ShulzLab/MORJ/electromechanical/3D_files/optical_rotary_joint/roller_bearing/outer_grove.SLDPRT

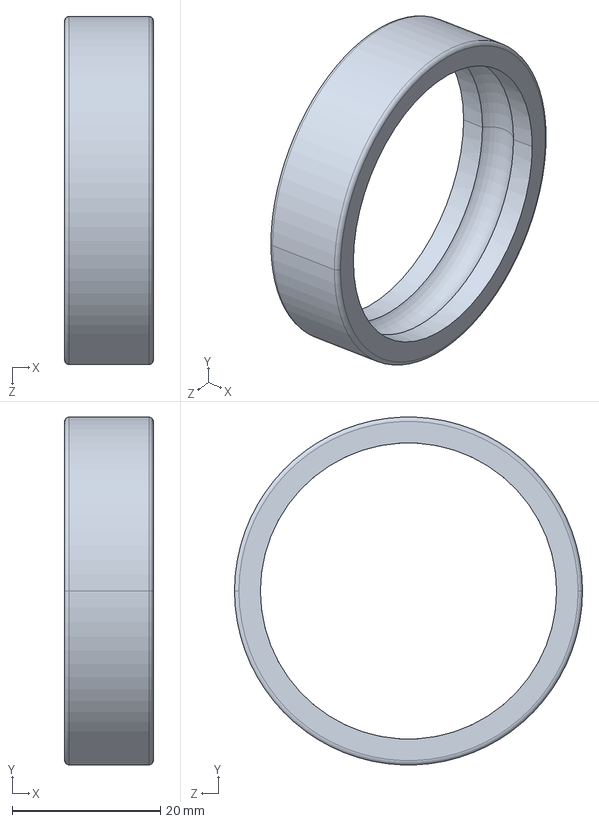
[picture p16: CAD file, 2022-12-15]
electromechanical/3D_files/optical_rotary_joint/roller_bearing/outer_grove.SLDPRT
12.0 x 47.0 x 47.0 mm
