ShulzLab/MORJ/electromechanical/3D_files/downstream_optical_assembly/Fiber_body.SLDPRT

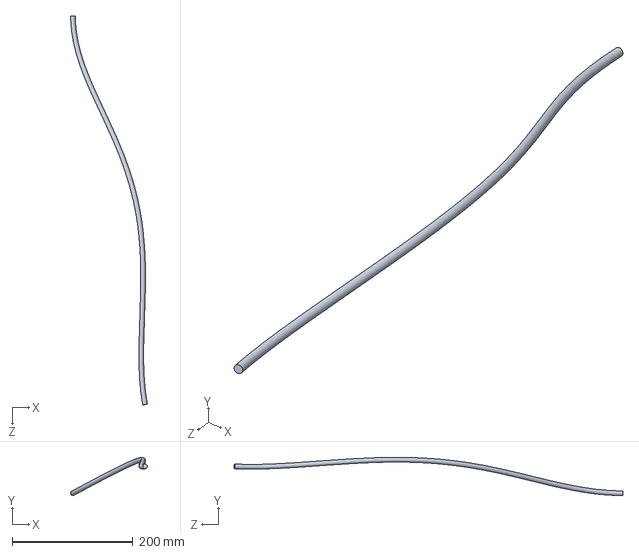
[picture p17: CAD file, 2022-12-15]
electromechanical/3D_files/downstream_optical_assembly/Fiber_body.SLDPRT
127.3 x 63.4 x 645.2 mm
