ShulzLab/MORJ/electromechanical/3D_files/electrical_rotary_joint/dovetail_fixed_body.SLDPRT

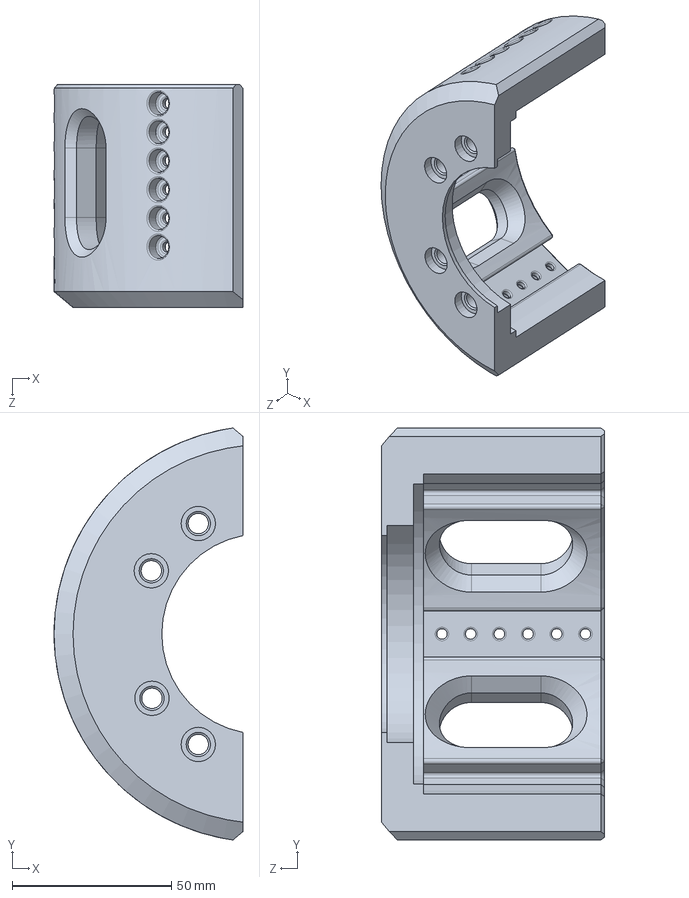
[picture p18: CAD file, 2022-12-15]
electromechanical/3D_files/electrical_rotary_joint/dovetail_fixed_body.SLDPRT
59.2 x 129.2 x 70.0 mm
