ShulzLab/MORJ/electromechanical/3D_files/motor_controller/proto_board.SLDPRT

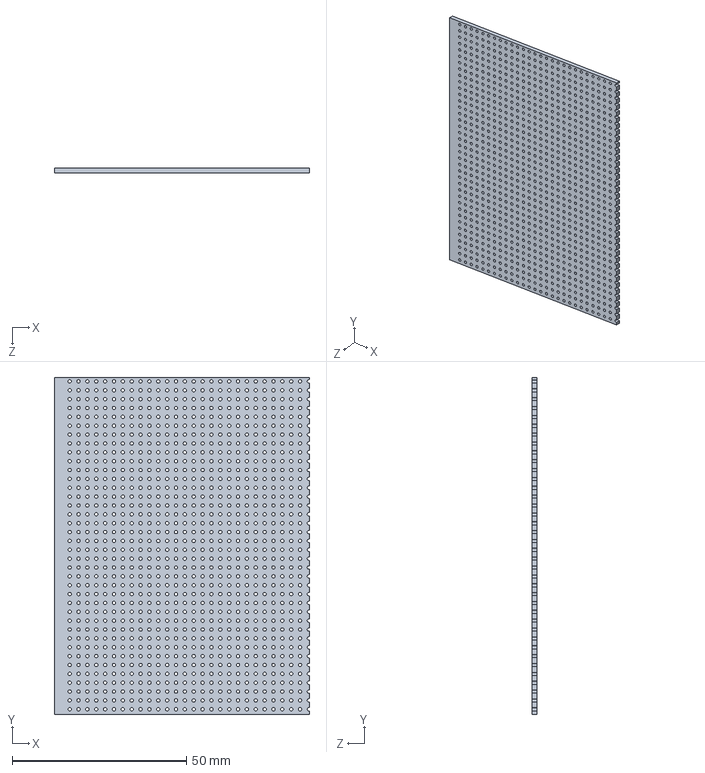
[picture p19: CAD file, 2022-12-15]
electromechanical/3D_files/motor_controller/proto_board.SLDPRT
73.2 x 96.6 x 1.54 mm
