ShulzLab/MORJ/electromechanical/3D_files/motor_system/Nema23_holder.SLDPRT

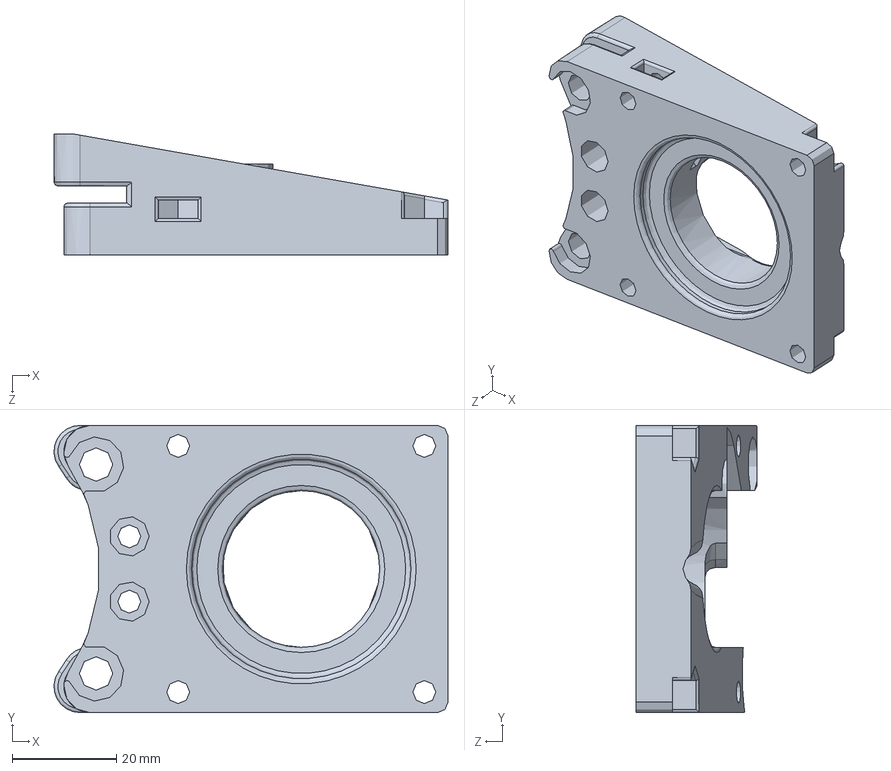
[picture p20: CAD file, 2022-12-15]
electromechanical/3D_files/motor_system/Nema23_holder.SLDPRT
75.5 x 55.0 x 23.2 mm
