ShulzLab/MORJ/electromechanical/3D_files/optical_rotary_joint/endplate.SLDPRT

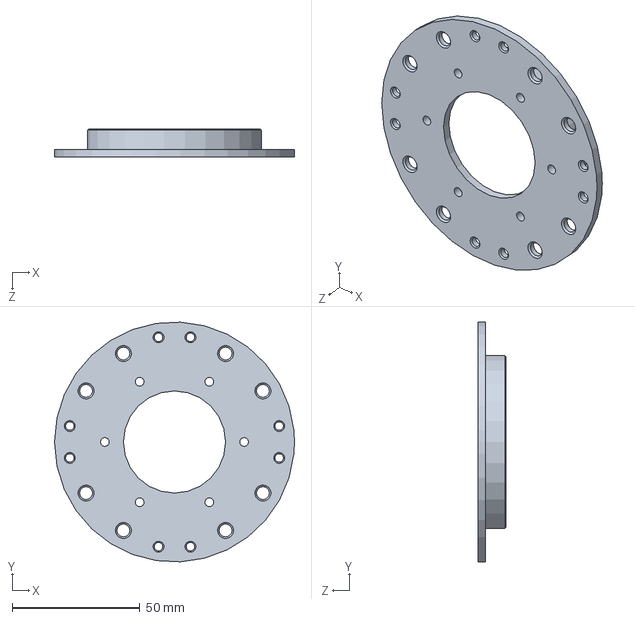
[picture p21: CAD file, 2022-12-15]
electromechanical/3D_files/optical_rotary_joint/endplate.SLDPRT
94.0 x 93.9 x 11.0 mm
