ShulzLab/MORJ/electromechanical/3D_files/upstream_optical_assembly/Lens.SLDPRT

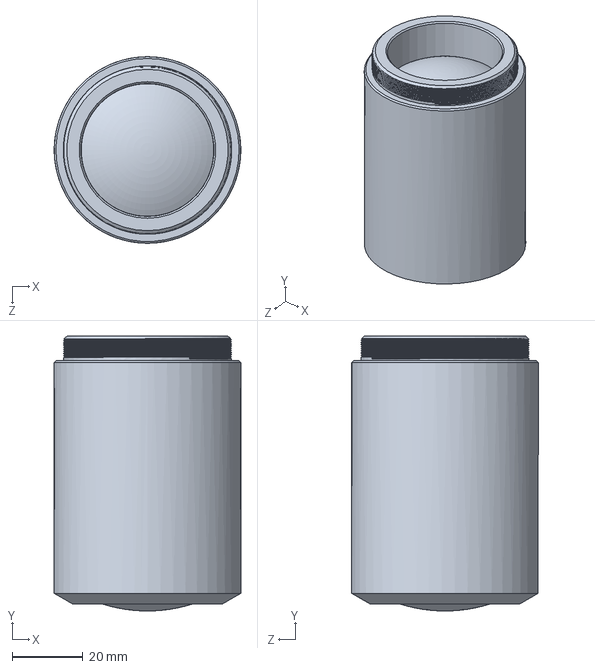
[picture p22: CAD file, 2022-12-15]
electromechanical/3D_files/upstream_optical_assembly/Lens.SLDPRT
52.9 x 78.0 x 52.9 mm
