ShulzLab/MORJ/electromechanical/3D_files/xyz_adjustment_system/focus_adjuster_proxy.SLDPRT

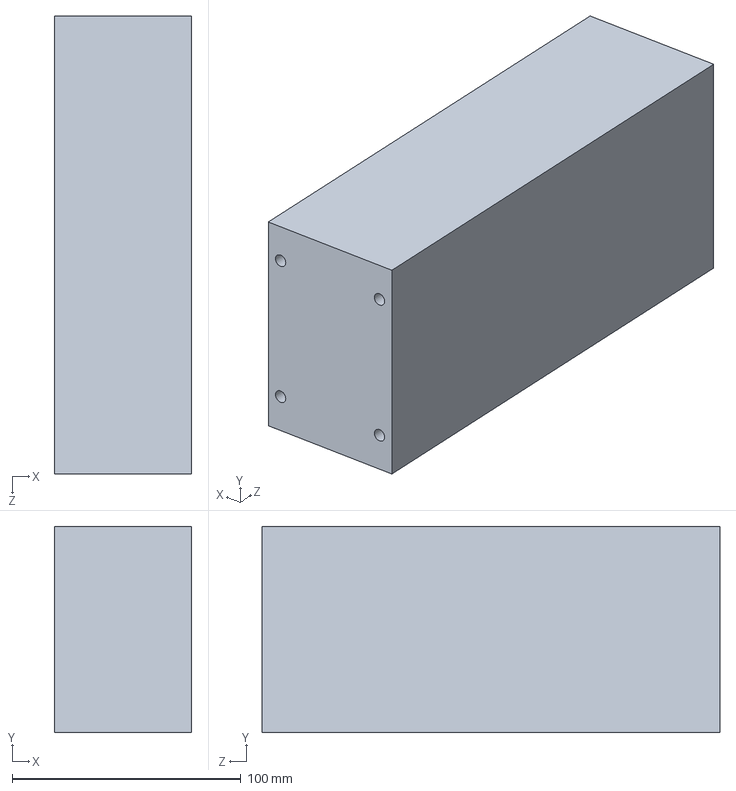
[picture p23: CAD file, 2022-12-15]
electromechanical/3D_files/xyz_adjustment_system/focus_adjuster_proxy.SLDPRT
60.0 x 90.0 x 200.0 mm
