ShulzLab/MORJ/electromechanical/3D_files/electrical_rotary_joint/dovetail_mobile_body.SLDPRT

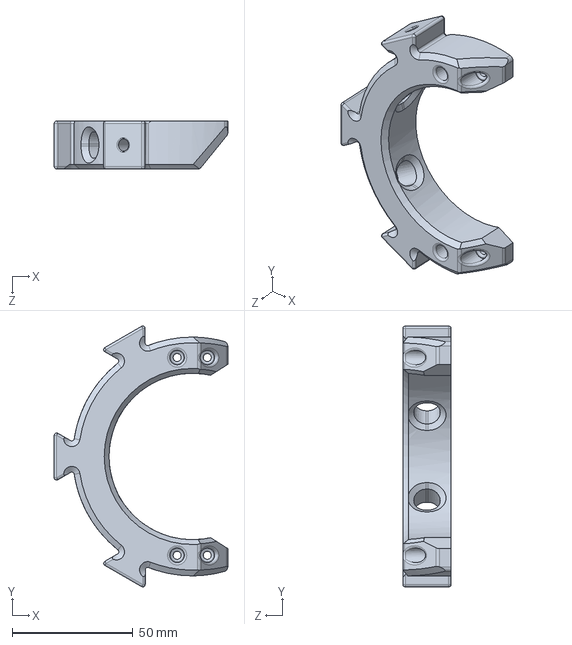
[picture p24: CAD file, 2022-12-15]
electromechanical/3D_files/electrical_rotary_joint/dovetail_mobile_body.SLDPRT
72.0 x 108.2 x 20.0 mm
