ShulzLab/MORJ/electromechanical/3D_files/motor_controller/connectors_opening_plate.SLDPRT

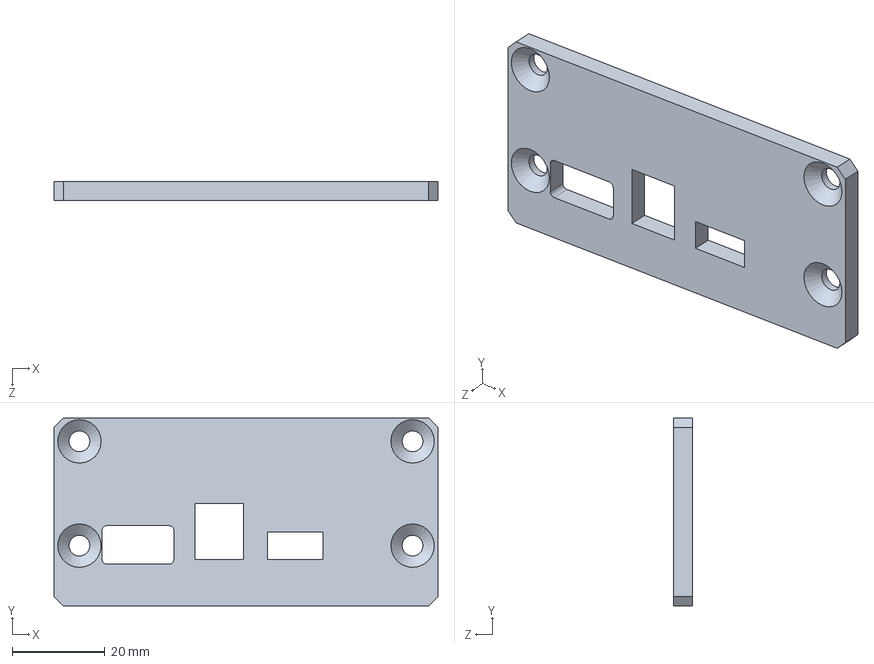
[picture p25: CAD file, 2022-12-15]
electromechanical/3D_files/motor_controller/connectors_opening_plate.SLDPRT
83.0 x 40.5 x 4.00 mm
