ShulzLab/MORJ/electromechanical/3D_files/motor_system/petitRoulementPlastique.SLDPRT

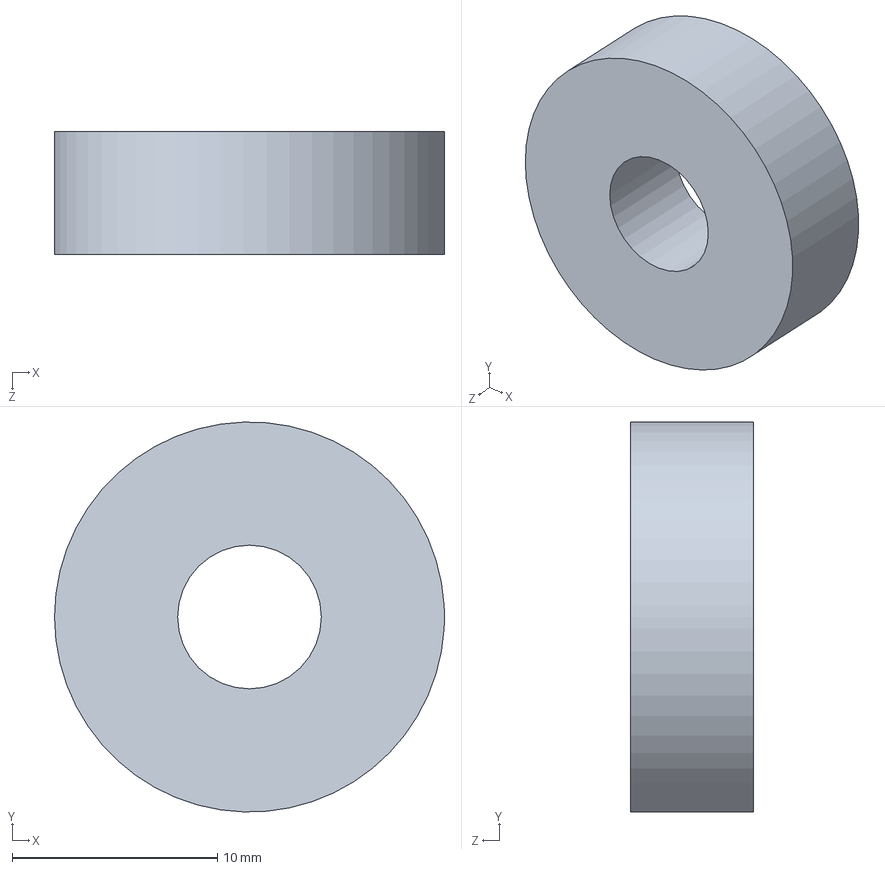
[picture p26: CAD file, 2022-12-15]
electromechanical/3D_files/motor_system/petitRoulementPlastique.SLDPRT
19.0 x 19.0 x 6.00 mm
