ShulzLab/MORJ/electromechanical/3D_files/optical_rotary_joint/roller_bearing/roller_ball.SLDPRT

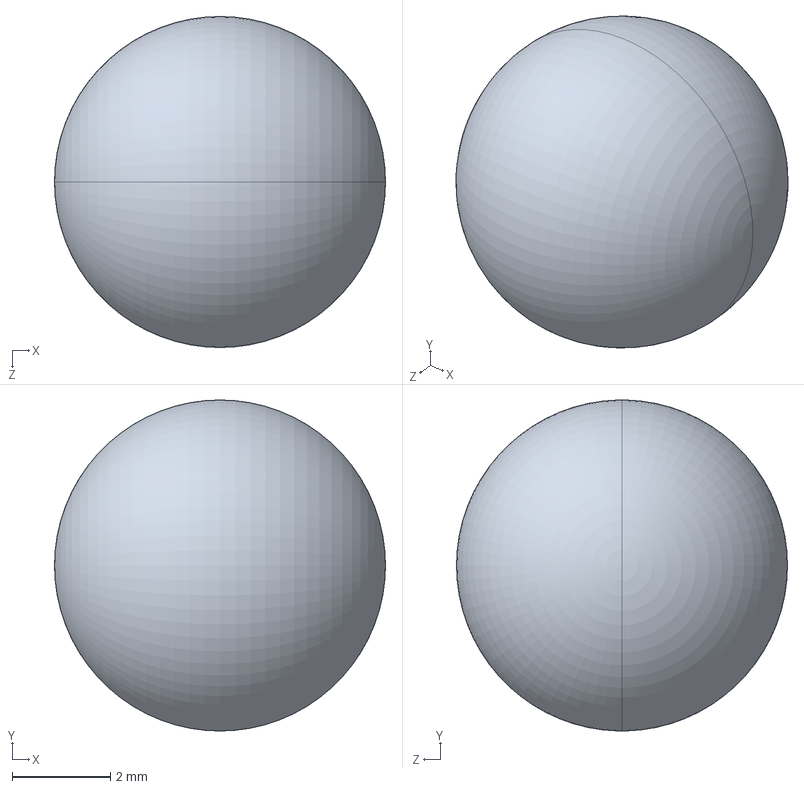
[picture p27: CAD file, 2022-12-15]
electromechanical/3D_files/optical_rotary_joint/roller_bearing/roller_ball.SLDPRT
6.75 x 6.75 x 6.75 mm
