ShulzLab/MORJ/electromechanical/3D_files/upstream_optical_assembly/Lens_hood.SLDPRT

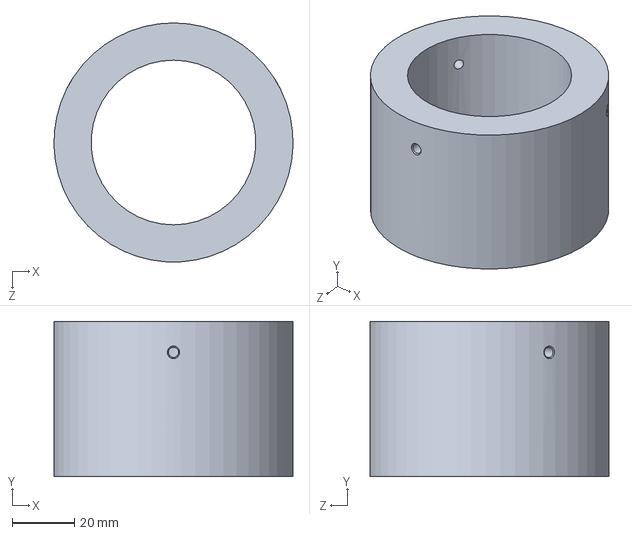
[picture p28: CAD file, 2022-12-15]
electromechanical/3D_files/upstream_optical_assembly/Lens_hood.SLDPRT
77.1 x 50.0 x 77.1 mm
