ShulzLab/MORJ/electromechanical/3D_files/xyz_adjustment_system/right_lateral_focus_holder.SLDPRT

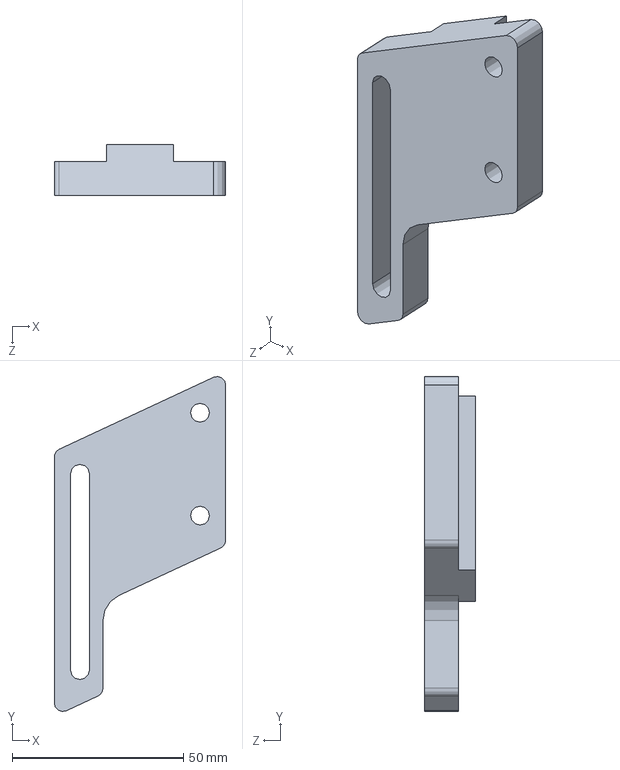
[picture p29: CAD file, 2022-12-15]
electromechanical/3D_files/xyz_adjustment_system/right_lateral_focus_holder.SLDPRT
50.0 x 97.7 x 15.0 mm
