ShulzLab/MORJ/electromechanical/3D_files/electrical_rotary_joint/driving_ring.SLDPRT

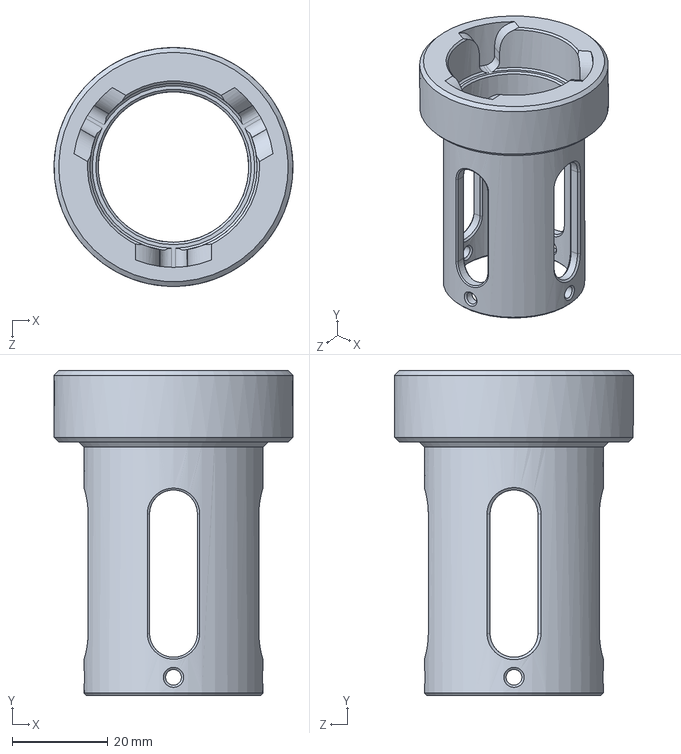
[picture p30: CAD file, 2022-12-15]
electromechanical/3D_files/electrical_rotary_joint/driving_ring.SLDPRT
50.0 x 68.0 x 50.0 mm
