ShulzLab/MORJ/electromechanical/3D_files/motor_controller/attachment_plate.SLDPRT

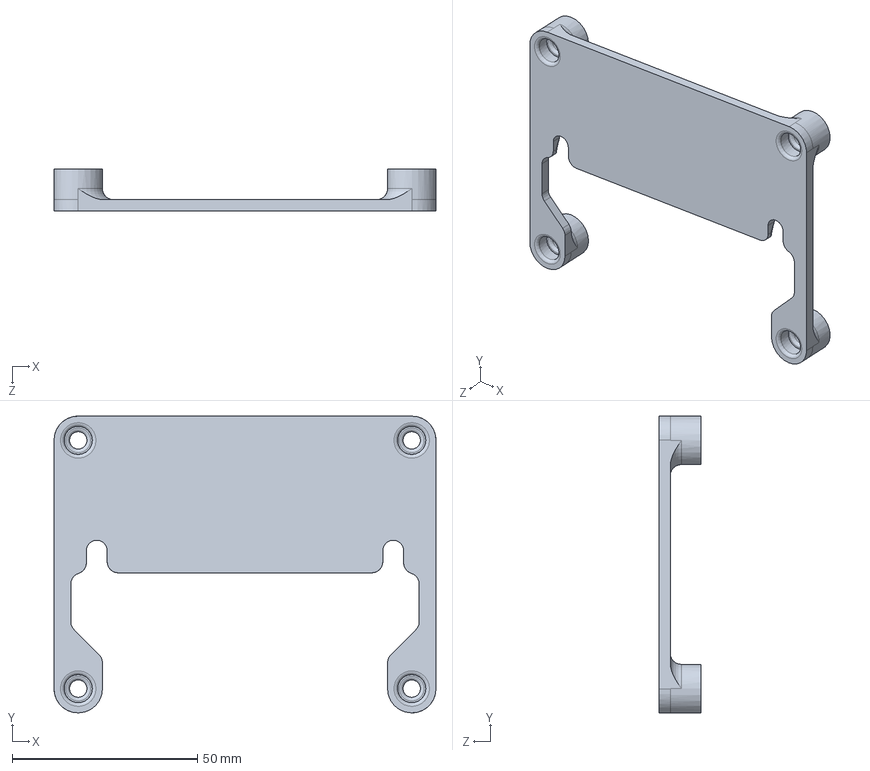
[picture p31: CAD file, 2022-12-15]
electromechanical/3D_files/motor_controller/attachment_plate.SLDPRT
103.1 x 80.1 x 11.2 mm
