ShulzLab/MORJ/electromechanical/3D_files/motor_system/StepperMotor_nema17.SLDPRT

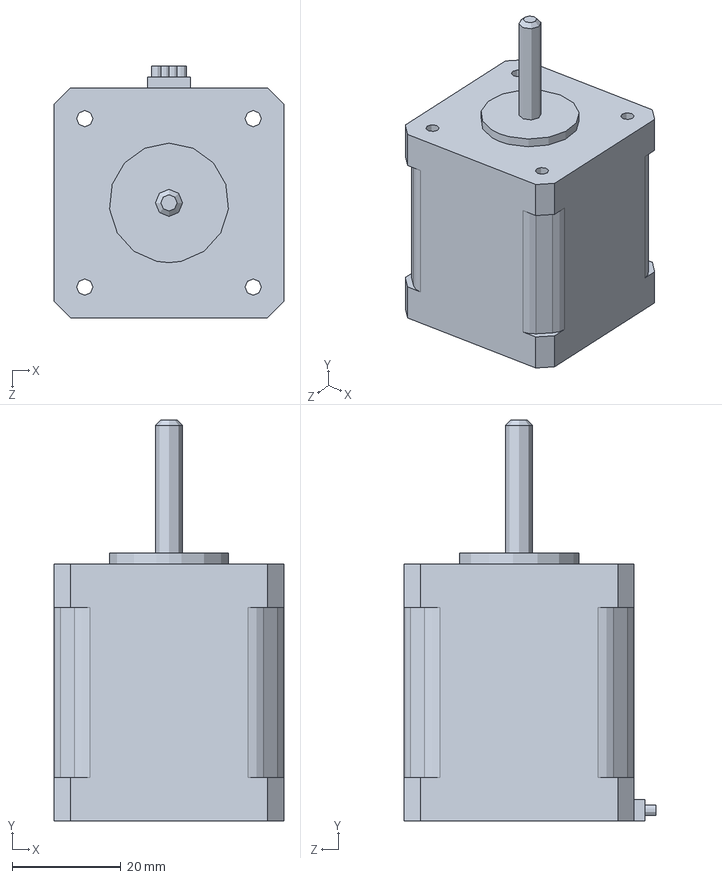
[picture p32: CAD file, 2022-12-15]
electromechanical/3D_files/motor_system/StepperMotor_nema17.SLDPRT
42.3 x 73.8 x 46.3 mm
