ShulzLab/MORJ/electromechanical/3D_files/optical_rotary_joint/roller_bearing/inner_grove.SLDPRT

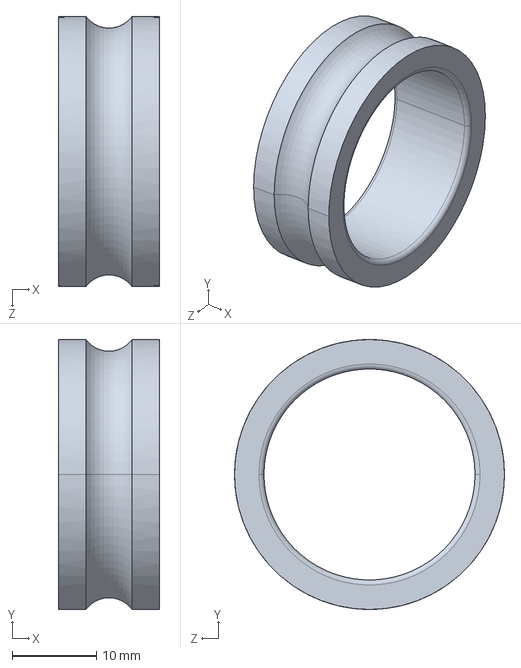
[picture p33: CAD file, 2022-12-15]
electromechanical/3D_files/optical_rotary_joint/roller_bearing/inner_grove.SLDPRT
12.0 x 32.0 x 32.0 mm
