ShulzLab/MORJ/electromechanical/3D_files/xyz_adjustment_system/BlocAdaptation.sldprt

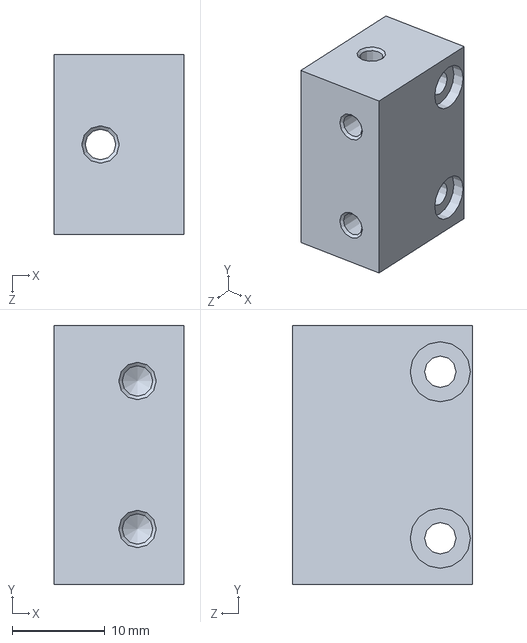
[picture p34: CAD file, 2022-12-15]
electromechanical/3D_files/xyz_adjustment_system/BlocAdaptation.sldprt
14.0 x 28.0 x 19.5 mm
