ShulzLab/MORJ/electromechanical/3D_files/electrical_rotary_joint/electrical_slip_ring_Jinpat_ LPT038-6.SLDPRT

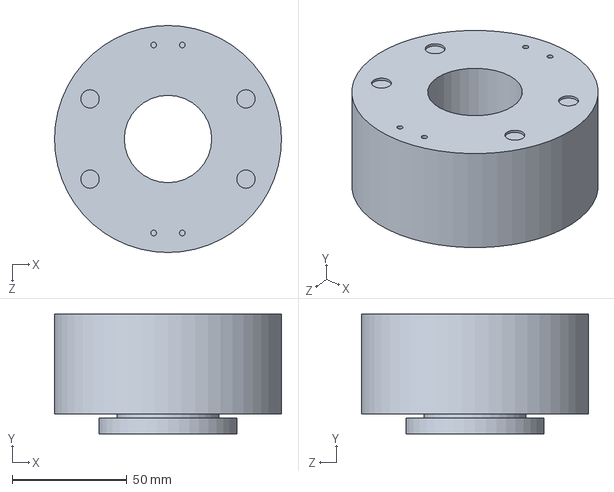
[picture p35: CAD file, 2022-12-15]
electromechanical/3D_files/electrical_rotary_joint/electrical_slip_ring_Jinpat_ LPT038-6.SLDPRT
99.0 x 52.3 x 99.0 mm
