ShulzLab/MORJ/electromechanical/3D_files/motor_controller/USB_port.SLDPRT

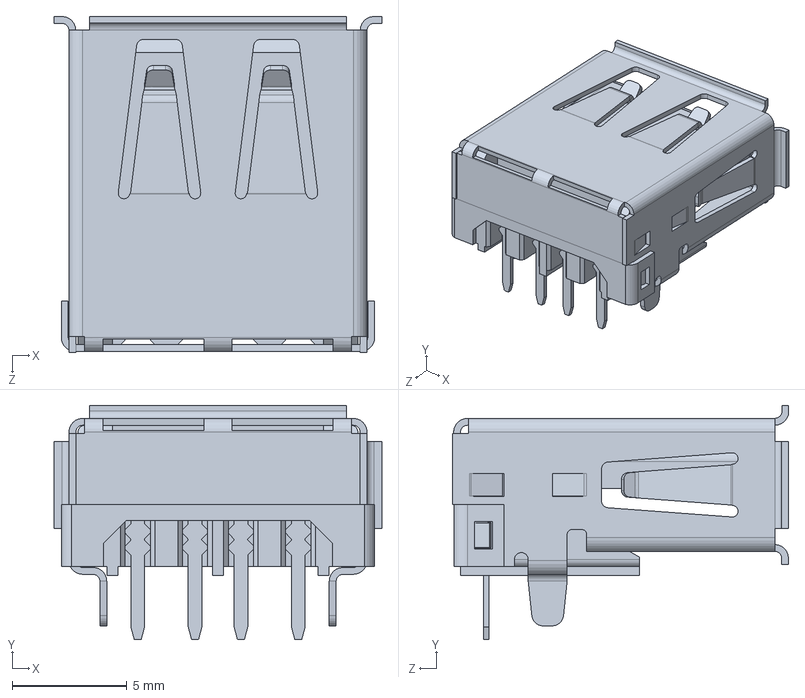
[picture p36: CAD file, 2022-12-15]
electromechanical/3D_files/motor_controller/USB_port.SLDPRT
14.3 x 10.2 x 14.6 mm
