ShulzLab/MORJ/electromechanical/3D_files/motor_system/Plot_Roulementplastique.SLDPRT

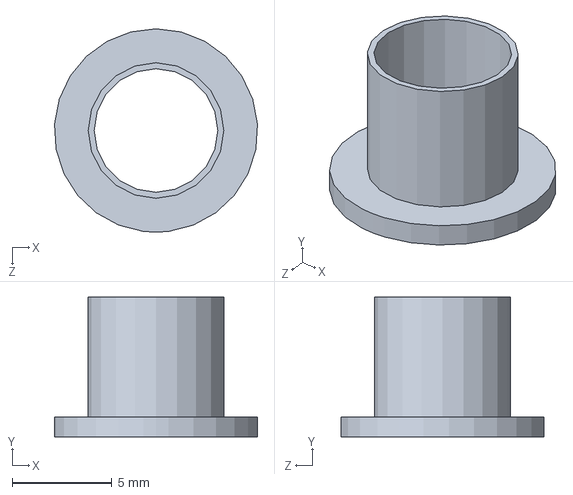
[picture p37: CAD file, 2022-12-15]
electromechanical/3D_files/motor_system/Plot_Roulementplastique.SLDPRT
10.2 x 7.00 x 10.2 mm
