ShulzLab/MORJ/electromechanical/3D_files/xyz_adjustment_system/Top_focus_holder.SLDPRT

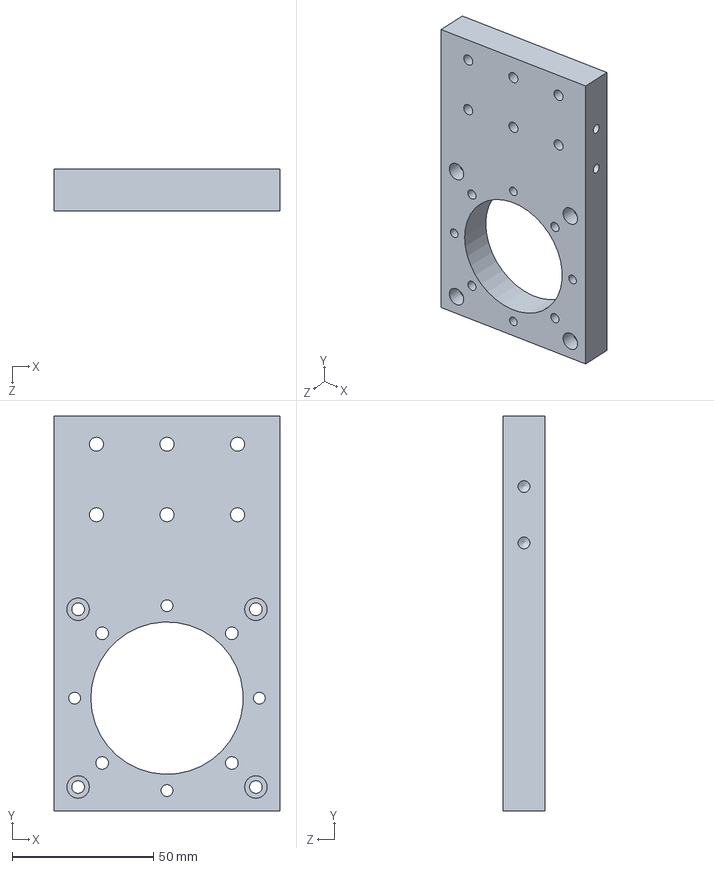
[picture p38: CAD file, 2022-12-15]
electromechanical/3D_files/xyz_adjustment_system/Top_focus_holder.SLDPRT
80.0 x 140.0 x 15.0 mm
