ShulzLab/MORJ/electromechanical/3D_files/optical_rotary_joint/adjustable_height_rotative_body.SLDPRT

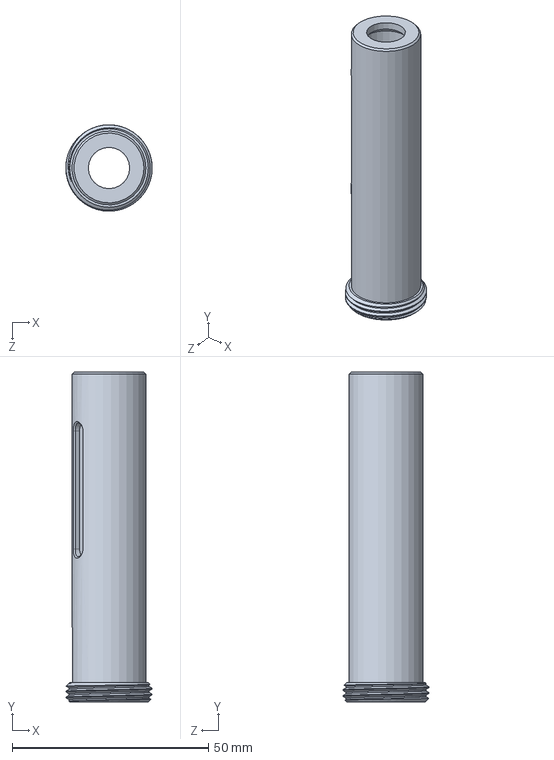
[picture p39: CAD file, 2022-12-15]
electromechanical/3D_files/optical_rotary_joint/adjustable_height_rotative_body.SLDPRT
22.0 x 84.0 x 22.0 mm
