ShulzLab/MORJ/electromechanical/3D_files/xyz_adjustment_system/Platine_Ajustement.SLDPRT

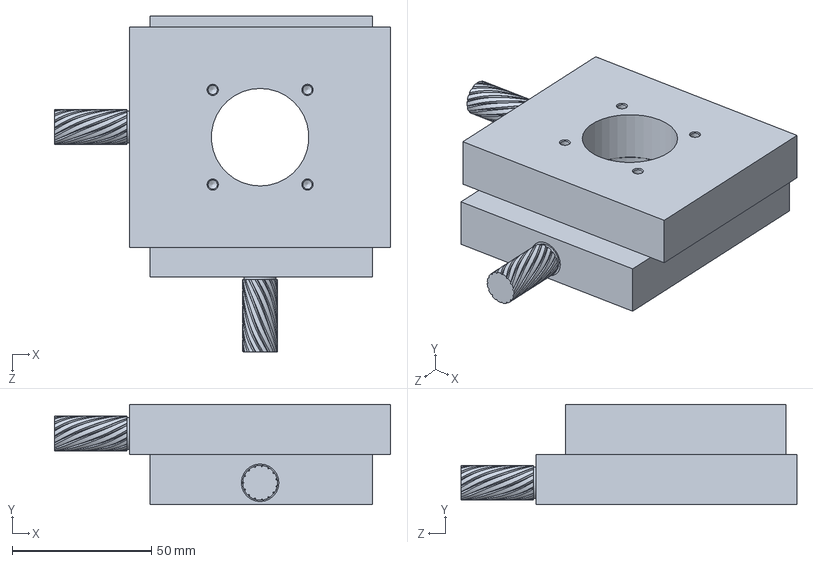
[picture p40: CAD file, 2022-12-15]
electromechanical/3D_files/xyz_adjustment_system/Platine_Ajustement.SLDPRT
120.7 x 36.0 x 120.6 mm
