ShulzLab/MORJ/electromechanical/3D_files/motor_controller/outer_case.SLDPRT

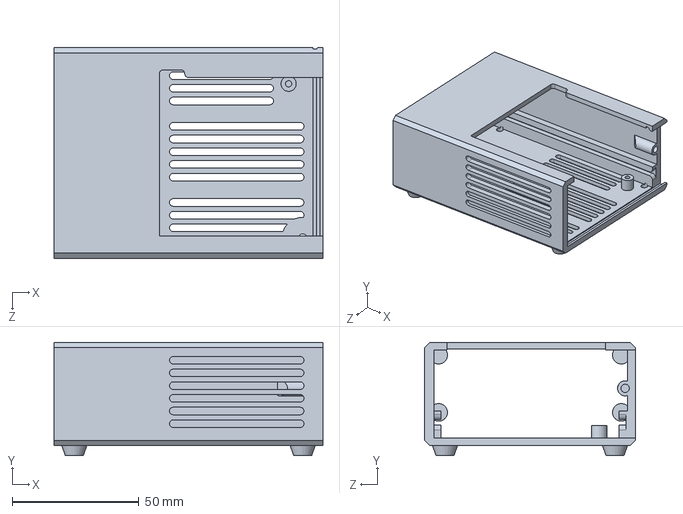
[picture p41: CAD file, 2022-12-15]
electromechanical/3D_files/motor_controller/outer_case.SLDPRT
106.0 x 44.5 x 83.0 mm
