ShulzLab/MORJ/electromechanical/3D_files/motor_system/Pulley GT2_60T.SLDPRT

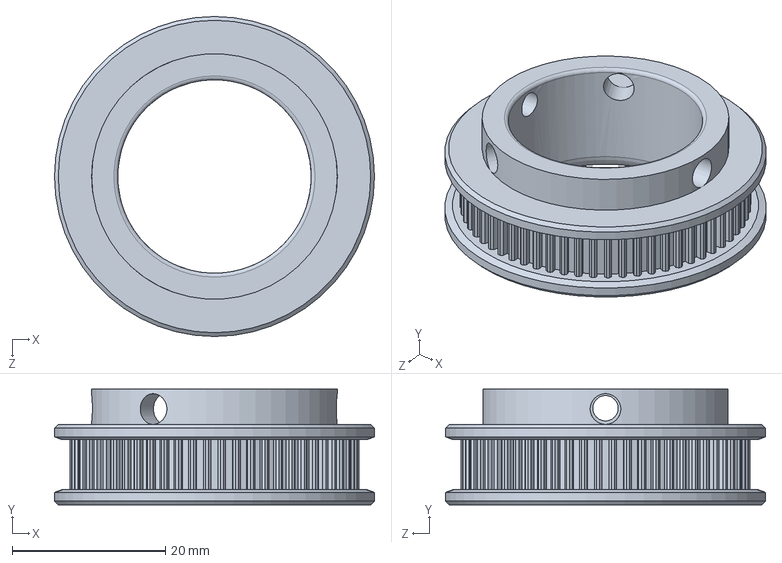
[picture p42: CAD file, 2022-12-15]
electromechanical/3D_files/motor_system/Pulley GT2_60T.SLDPRT
41.7 x 15.1 x 41.7 mm
