ShulzLab/MORJ/electromechanical/3D_files/optical_rotary_joint/spacer.SLDPRT

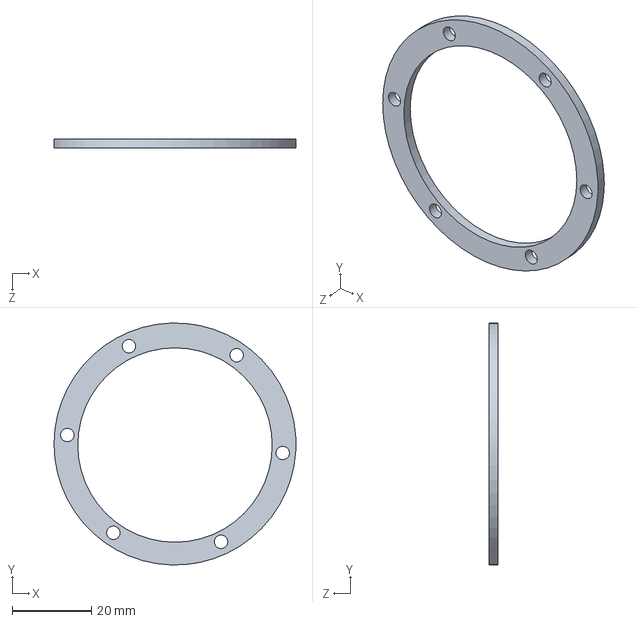
[picture p43: CAD file, 2022-12-15]
electromechanical/3D_files/optical_rotary_joint/spacer.SLDPRT
61.0 x 61.0 x 2.30 mm
