ShulzLab/MORJ/electromechanical/3D_files/xyz_adjustment_system/Bottom_focus_holder.SLDPRT

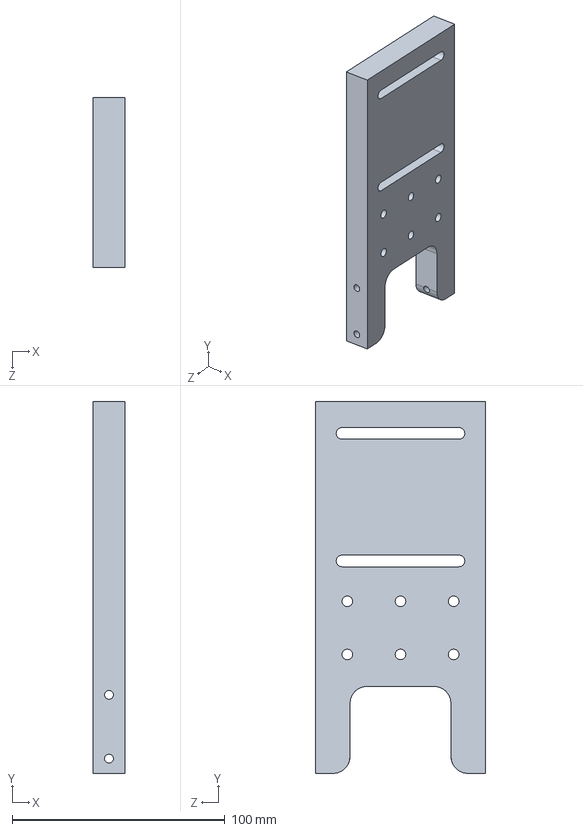
[picture p44: CAD file, 2022-12-15]
electromechanical/3D_files/xyz_adjustment_system/Bottom_focus_holder.SLDPRT
15.0 x 175.0 x 80.0 mm
