ShulzLab/MORJ/electromechanical/3D_files/motor_controller/Fan_Case.SLDPRT

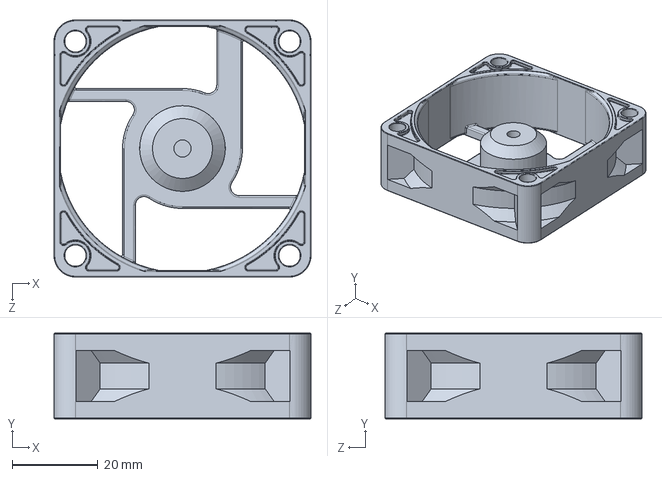
[picture p45: CAD file, 2022-12-15]
electromechanical/3D_files/motor_controller/Fan_Case.SLDPRT
60.0 x 20.0 x 60.0 mm
