ShulzLab/MORJ/electromechanical/3D_files/motor_system/Nema17_holder.SLDPRT

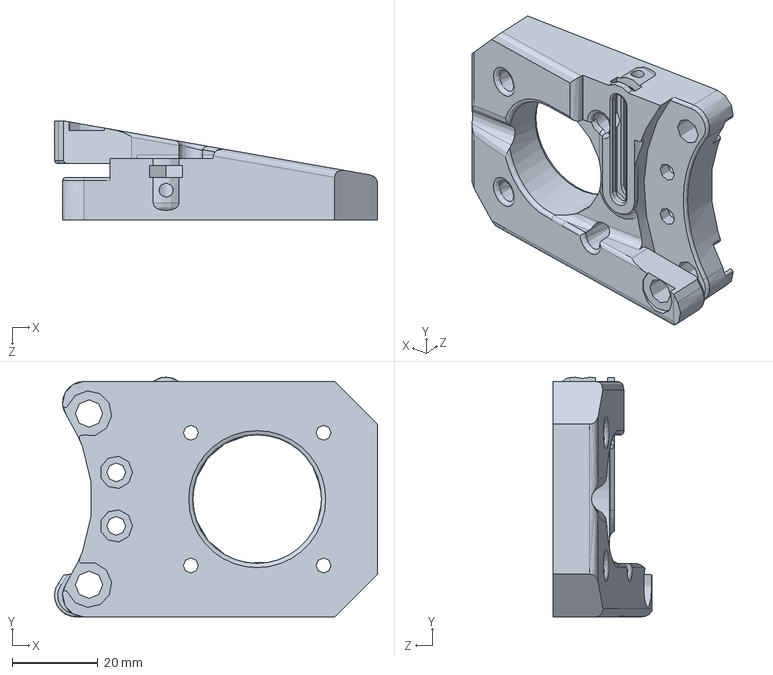
[picture p46: CAD file, 2022-12-15]
electromechanical/3D_files/motor_system/Nema17_holder.SLDPRT
75.5 x 56.0 x 23.2 mm
