ShulzLab/MORJ/electromechanical/3D_files/xyz_adjustment_system/PlaqueInterne_LENS.sldprt

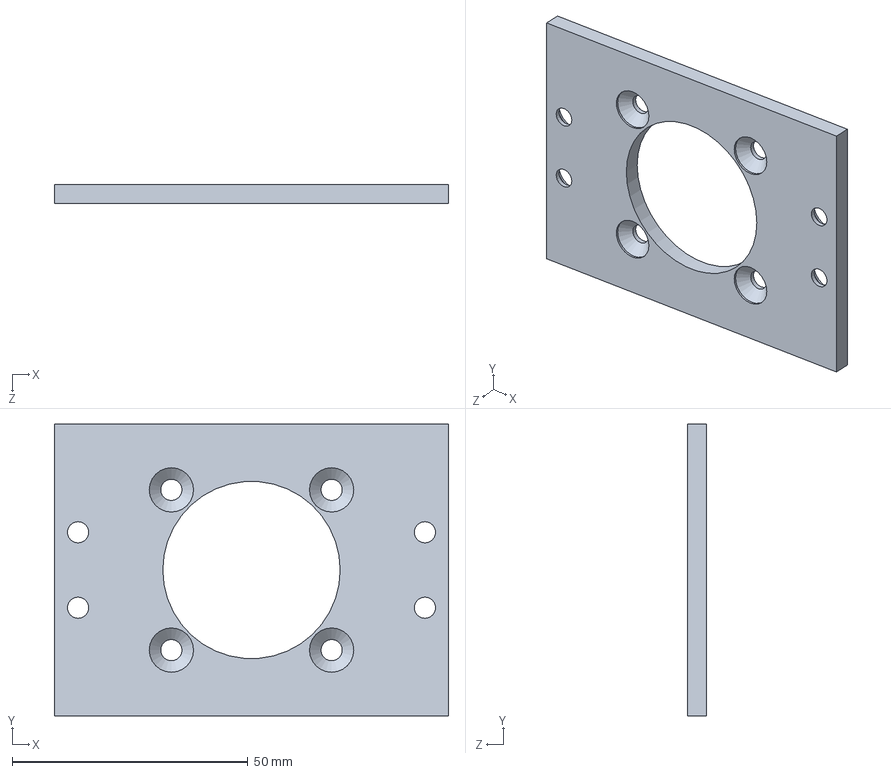
[picture p47: CAD file, 2022-12-15]
electromechanical/3D_files/xyz_adjustment_system/PlaqueInterne_LENS.sldprt
83.6 x 61.9 x 4.00 mm
