ShulzLab/MORJ/electromechanical/3D_files/motor_system/transmission_belt.SLDPRT

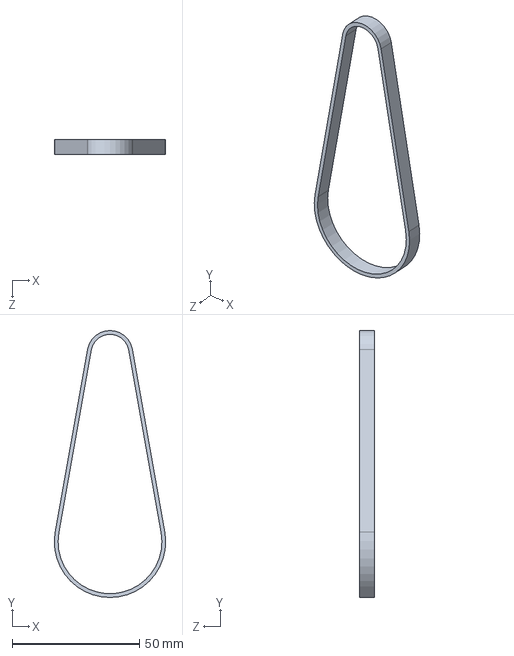
[picture p48: CAD file, 2022-12-15]
electromechanical/3D_files/motor_system/transmission_belt.SLDPRT
43.7 x 104.7 x 6.00 mm
