ShulzLab/MORJ/electromechanical/3D_files/motor_controller/Fan.SLDPRT

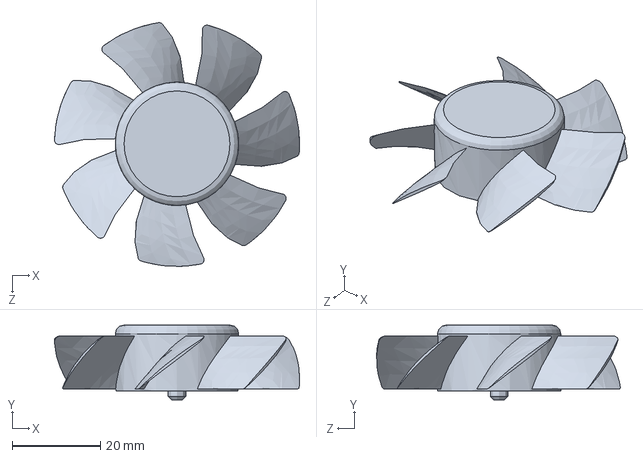
[picture p49: CAD file, 2022-12-15]
electromechanical/3D_files/motor_controller/Fan.SLDPRT
55.6 x 17.0 x 55.3 mm
