ShulzLab/MORJ/electromechanical/3D_files/motor_controller/fan_adapter.SLDPRT

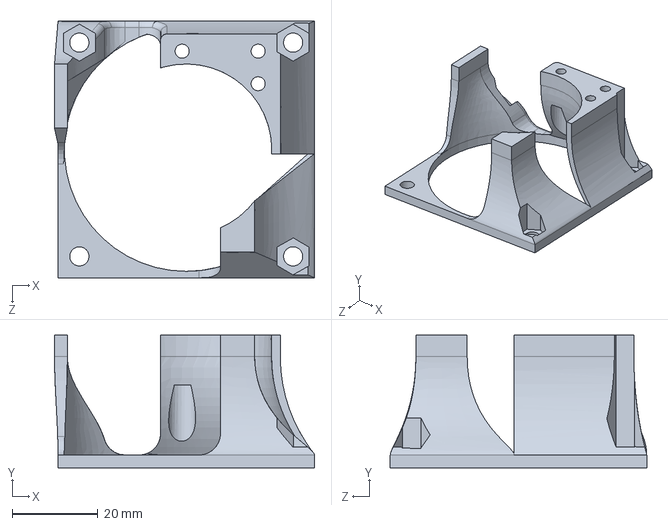
[picture p50: CAD file, 2022-12-15]
electromechanical/3D_files/motor_controller/fan_adapter.SLDPRT
60.8 x 31.0 x 60.0 mm
